juniperlynx/Christmas-2019/Graphics/B.png

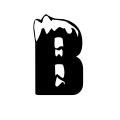
Graphics/B.png
