juniperlynx/Christmas-2019/Software/christmasfont.h

// Font header for a Christmas card with a Charlieplexed display
// By:   _           _               
//      (_)_  _ _ _ (_)_ __  ___ _ _ 
//      | | || | ' \| | '_ \/ -_) '_|
//     _/ |\_,_|_||_|_| .__/\___|_|  
//    |__/            |_|  
// Filename: christmasfont.h
// Date: Nov 24, 2019

#ifndef CHRISTMASFONT_H
#define CHRISTMASFONT_H

// Declare font array constant, Follows ASCII with omissions
const uint8_t font[95][3] = {
    // NUL [0] to US [31] are unprintable characters
    {0x00, 0x00, 0x00}, // Space [32]
    {0x00, 0x1D, 0x00}, // ! [33]
    {0x18, 0x00, 0x18}, // " [34]
    {0x1F, 0x0A, 0x1F}, // # [35]
    {0x09, 0x1F, 0x12}, // $ [36]
    {0x13, 0x04, 0x19}, // % [37]
    {0x0A, 0x15, 0x0B}, // & [38]
    {0x00, 0x18, 0x00}, // ' [39]
    {0x00, 0x0E, 0x11}, // ( [40]
    {0x11, 0x0E, 0x00}, // ) [41]
    {0x04, 0x0A, 0x04}, // * [42]
    {0x04, 0x0E, 0x04}, // + [43]
    {0x01, 0x02, 0x00}, // , [44]
    {0x04, 0x04, 0x04}, // - [45]
    {0x00, 0x01, 0x00}, // . [46]
    {0x03, 0x04, 0x18}, // / [47]
    {0x1F, 0x11, 0x1F}, // 0 [48]
    {0x09, 0x1F, 0x01}, // 1 [49]
    {0x13, 0x15, 0x09}, // 2 [50]
    {0x11, 0x15, 0x0A}, // 3 [51]
    {0x1C, 0x04, 0x1F}, // 4 [52]
    {0x19, 0x15, 0x12}, // 5 [53]
    {0x0E, 0x15, 0x12}, // 6 [54]
    {0x13, 0x14, 0x18}, // 7 [55]
    {0x0A, 0x15, 0x0A}, // 8 [56]
    {0x09, 0x15, 0x0E}, // 9 [57]
    {0x00, 0x0A, 0x00}, // : [58]
    {0x01, 0x0A, 0x00}, // ; [59]
    {0x04, 0x0A, 0x11}, // < [60]
    {0x0A, 0x0A, 0x0A}, // = [61]
    {0x11, 0x0A, 0x04}, // > [62]
    {0x10, 0x15, 0x08}, // ? [39]
    {0x0E, 0x15, 0x1D}, // @ [64]
    {0x0F, 0x14, 0x0F}, // A [65]
    {0x1F, 0x15, 0x0A}, // B [66]
    {0x0E, 0x11, 0x11}, // C [67]
    {0x1F, 0x11, 0x0E}, // D [68]
    {0x1F, 0x15, 0x11}, // E [69]
    {0x1F, 0x14, 0x10}, // F [70]
    {0x0E, 0x11, 0x16}, // G [71]
    {0x1F, 0x04, 0x1F}, // H [72]
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
    // DEL [127] is unprintable
};
#endif
